Lait236/DIPLOM_LAB_STAND/DIPLOM_LAB_STAND/screens/servo_test/servo_test.h

/*
 * servo_test.h
 *
 * Created: 14.04.2026 23:35:36
 *  Author: Владислав
 */ 


#ifndef SERVO_TEST_H_
#define SERVO_TEST_H_

void screen_servo_test_start(void); // открываем экран теста сервопривода
void screen_servo_test_key(char key); // обрабатываем кнопку на экране теста сервопривода

#endif /* SERVO_TEST_H_ */
