Lait236/DIPLOM_LAB_STAND/DIPLOM_LAB_STAND/screens/stepper_test/stepper_test.h

/*
 * stepper_test.h
 *
 * Created: 22.04.2026 0:28:15
 *  Author: Владислав
 */ 


#ifndef STEPPER_TEST_H_
#define STEPPER_TEST_H_

void screen_stepper_test_start(void); // открываем экран теста шагового мотора
void screen_stepper_test_key(char key); // обрабатываем клавишу на экране теста шагового мотора

#endif /* STEPPER_TEST_H_ */
